cdrfiuba/tito/Placas/Placa_Tito_2011/Placa_1_sensor/placa1sensor.sch

## KiCad design Placas/Placa_Tito_2011/Placa_1_sensor/placa1sensor.sch (2011-11-02)

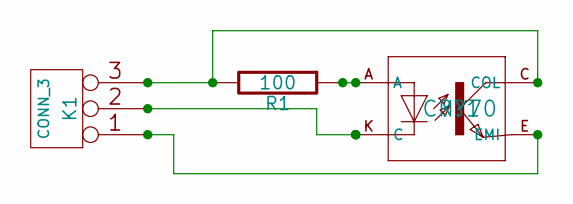
[picture p5: schematic placa1sensor.sch]

Parts:
??1: CNY70
K1: CONN_3
R1: 100

Connections:
unnamed: ??1.A, R1.1
unnamed: ??1.C (COL), K1.3, R1.2
unnamed: ??1.E (EMI), K1.1
unnamed: ??1.K (C), K1.2 (PM)
