cdrfiuba/tito/Placas/Placa_Tito_2011/Placa_principal/placa_principal.sch

## KiCad design Placas/Placa_Tito_2011/Placa_principal/placa_principal.sch (2013-02-23)

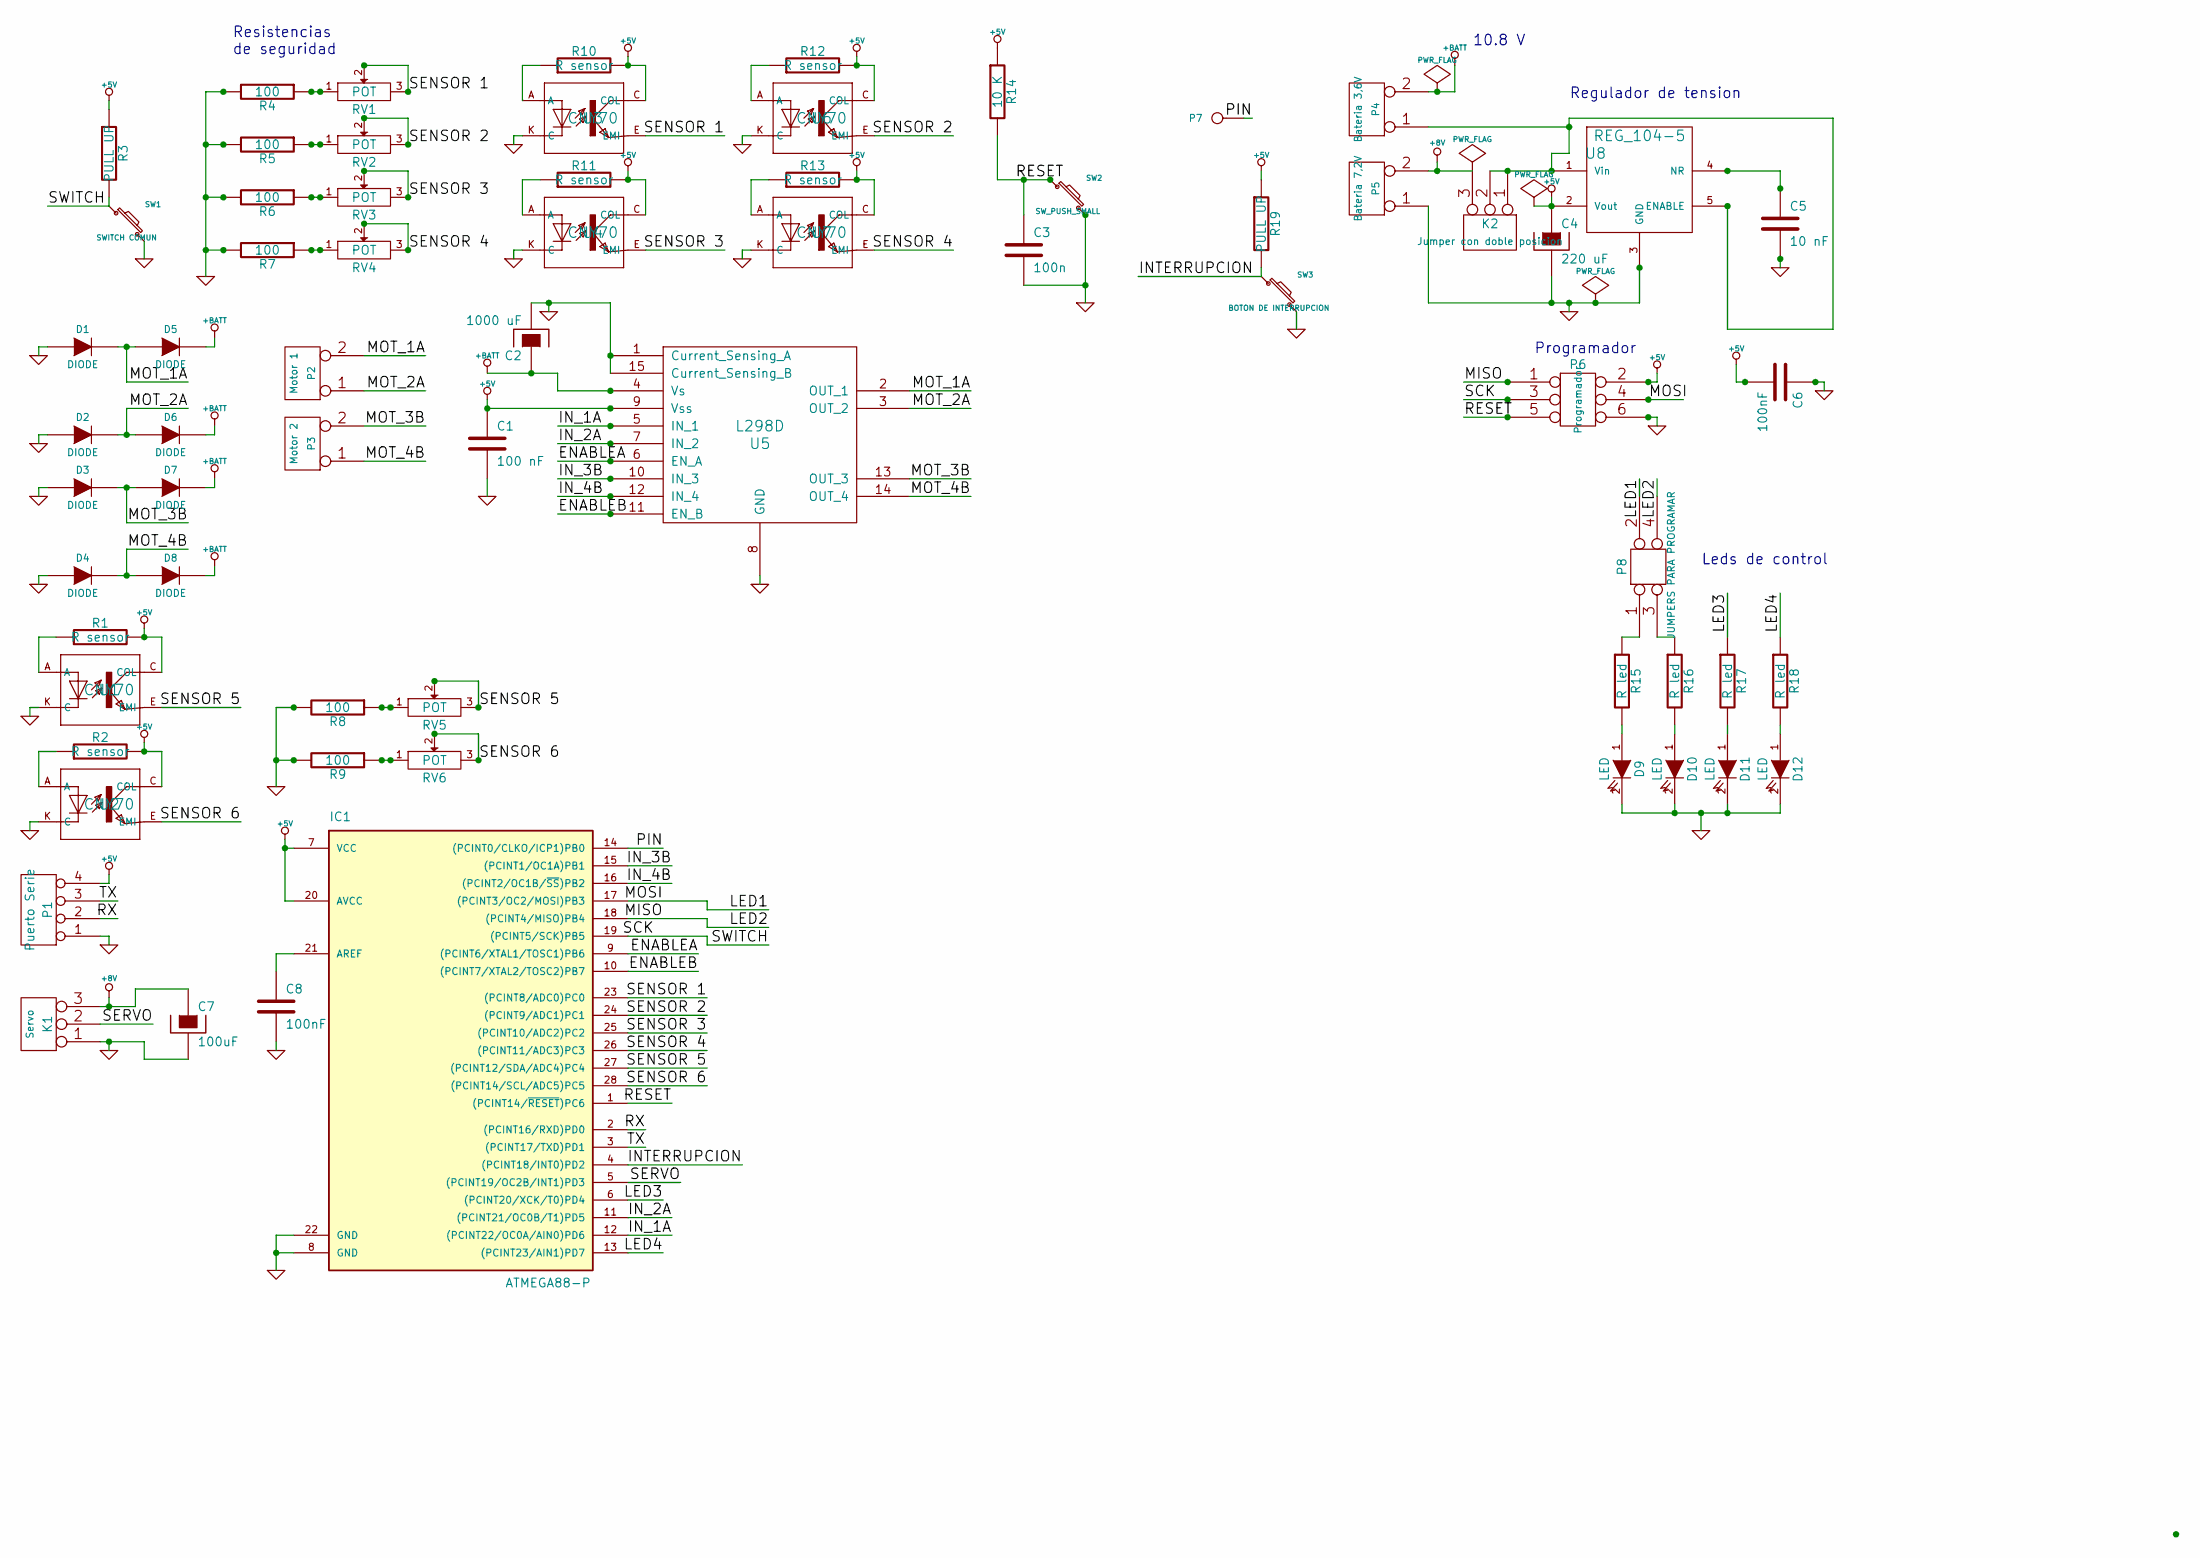
[picture p6: schematic placa_principal.sch]

Parts:
C1: 100 nF
C2: 1000 uF
C3: 100n
C4: 220 uF
C5: 10 nF
C6, C8: 100nF
C7: 100uF
D1, D2, D3, D4, D5, D6, D7, D8: DIODE
D9, D10, D11, D12: LED
IC1: ATMEGA88-P; DIL28
K1: Servo
K2: Jumper con doble posicion
P1: Puerto Serie
P2: Motor 1
P3: Motor 2
P4: Bateria 3,6V
P5: Bateria 7,2V
P6: Programador
P7: CONN_1
P8: JUMPERS PARA PROGRAMAR
R1, R2, R10, R11, R12, R13: R sensor
R3, R19: PULL UP
R4, R5, R6, R7, R8, R9: 100
R14: 10 K
R15, R16, R17, R18: R led
RV1, RV2, RV3, RV4, RV5, RV6: POT
SW1: SWITCH COMUN
SW2: SW_PUSH_SMALL
SW3: BOTON DE INTERRUPCION
U1, U2, U3, U4, U6, U7: CNY70
U5: L298D
U8: REG_104-5

Connections:
+5V: C1.1, C4.1, C6.2, IC1.7 (VCC), IC1.20 (AVCC), P1.4, P6.2, R1.2, R2.2, R3.1, R10.2, R11.2, R12.2, R13.2, R14.1, R19.1, U1.C (COL), U2.C (COL), U3.C (COL), U4.C (COL), U5.9 (Vss), U6.C (COL), U7.C (COL), U8.2 (Vout)
+8V: C7.1, K1.3, K2.3, P5.2 (PM)
+BATT: C2.1, D5.2 (K), D6.2 (K), D7.2 (K), D8.2 (K), P4.2 (PM), U5.4 (Vs)
ENABLEA: IC1.9 ((PCINT6/XTAL1/TOSC1)PB6), U5.6 (EN_A)
ENABLEB: IC1.10 ((PCINT7/XTAL2/TOSC2)PB7), U5.11 (EN_B)
GND: C1.2, C2.2, C3.2, C4.2, C5.2, C6.1, C7.2, C8.2, D1.1 (A), D2.1 (A), D3.1 (A), D4.1 (A), D9.2 (K), D10.2 (K), D11.2 (K), D12.2 (K), IC1.8 (GND), IC1.22 (GND), K1.1, P1.1, P5.1, P6.6, R4.2, R5.2, R6.2, R7.2, R8.2, R9.2, SW1.2, SW2.2, SW3.2, U1.K (C), U2.K (C), U3.K (C), U4.K (C), U5.1 (Current_Sensing_A), U5.8 (GND), U5.15 (Current_Sensing_B), U6.K (C), U7.K (C), U8.3 (GND)
INTERRUPCION: IC1.4 ((PCINT18/INT0)PD2), R19.2, SW3.1
IN_1A: IC1.12 ((PCINT22/OC0A/AIN0)PD6), U5.5 (IN_1)
IN_2A: IC1.11 ((PCINT21/OC0B/T1)PD5), U5.7 (IN_2)
IN_3B: IC1.15 ((PCINT1/OC1A)PB1), U5.10 (IN_3)
IN_4B: IC1.16 ((PCINT2/OC1B/~SS~)PB2), U5.12 (IN_4)
LED1: IC1.17 ((PCINT3/OC2/MOSI)PB3), P6.4, P8.2
LED2: IC1.18 ((PCINT4/MISO)PB4), P6.1, P8.4
LED3: IC1.6 ((PCINT20/XCK/T0)PD4), R17.1
LED4: IC1.13 ((PCINT23/AIN1)PD7), R18.1
MOT_1A: D1.2 (K), D5.1 (A), P2.2 (PM), U5.2 (OUT_1)
MOT_2A: D2.2 (K), D6.1 (A), P2.1, U5.3 (OUT_2)
MOT_3B: D3.2 (K), D7.1 (A), P3.2 (PM), U5.13 (OUT_3)
MOT_4B: D4.2 (K), D8.1 (A), P3.1, U5.14 (OUT_4)
unnamed: C5.1, U8.4 (NR)
unnamed: C8.1, IC1.21 (AREF)
unnamed: D9.1 (A), R15.2
unnamed: D10.1 (A), R16.2
unnamed: D11.1 (A), R17.2
unnamed: D12.1 (A), R18.2
unnamed: K2.1, K2.2 (PM), P4.1, U8.1 (Vin), U8.5 (ENABLE)
unnamed: P8.1, R15.1
unnamed: P8.3, R16.1
unnamed: R1.1, U1.A
unnamed: R2.1, U2.A
unnamed: R4.1, RV1.1
unnamed: R5.1, RV2.1
unnamed: R6.1, RV3.1
unnamed: R7.1, RV4.1
unnamed: R8.1, RV5.1
unnamed: R9.1, RV6.1
unnamed: R10.1, U3.A
unnamed: R11.1, U4.A
unnamed: R12.1, U6.A
unnamed: R13.1, U7.A
PIN: IC1.14 ((PCINT0/CLKO/ICP1)PB0), P7.1
RESET: C3.1, IC1.1 ((PCINT14/~RESET~)PC6), P6.5, R14.2, SW2.1
RX: IC1.2 ((PCINT16/RXD)PD0), P1.2
SCK: IC1.19 ((PCINT5/SCK)PB5), P6.3, R3.2, SW1.1
SENSOR 1: IC1.23 ((PCINT8/ADC0)PC0), RV1.2, RV1.3, U3.E (EMI)
SENSOR 2: IC1.24 ((PCINT9/ADC1)PC1), RV2.2, RV2.3, U6.E (EMI)
SENSOR 3: IC1.25 ((PCINT10/ADC2)PC2), RV3.2, RV3.3, U4.E (EMI)
SENSOR 4: IC1.26 ((PCINT11/ADC3)PC3), RV4.2, RV4.3, U7.E (EMI)
SENSOR 5: IC1.27 ((PCINT12/SDA/ADC4)PC4), RV5.2, RV5.3, U1.E (EMI)
SENSOR 6: IC1.28 ((PCINT14/SCL/ADC5)PC5), RV6.2, RV6.3, U2.E (EMI)
SERVO: IC1.5 ((PCINT19/OC2B/INT1)PD3), K1.2 (PM)
TX: IC1.3 ((PCINT17/TXD)PD1), P1.3

Notes on the sheet:
Programador
Resistencias de seguridad
10.8 V
Leds de control
Regulador de tension
