cdrfiuba/tito/SRC/Codigo Tito 2.0/tito.h

#ifndef HEADER_TITO
#define HEADER_TITO

/**
 Prototipos
*/
void startup (void);
//void prueba_frenado(void);

/**
 estados y eventos para la fsm
*/
typedef enum estados {
    
    ST_EN_LINEA = 0,

    ST_YENDOSE_POCO_POR_DERECHA = 1,
    ST_YENDOSE_MUCHO_POR_DERECHA = 2,
    ST_AFUERA_POR_DERECHA = 3,
    ST_VOLVIENDO_POR_DERECHA = 4,
    ST_VOLVIO_POR_DERECHA = 5,

    ST_YENDOSE_POCO_POR_IZQUIERDA = 6,
    ST_YENDOSE_MUCHO_POR_IZQUIERDA = 7,
    ST_AFUERA_POR_IZQUIERDA = 8,
    ST_VOLVIENDO_POR_IZQUIERDA = 9,
    ST_VOLVIO_POR_IZQUIERDA = 10,
    
    ST_MAX_ESTADOS = 11

} estados_t;
typedef enum estados_resumidos {
    EL=0,

    YPPD=1,
    YMPD=2,
    APD=3,
    VEPD=4,
    VOPD=5,

    YPPI=6,
    YMPI=7,
    API=8,
    VEPI=9,
    VOPI=10,

    ME=11
} estados_resumidos_t;
// (los sensores se componen como:
//  CURVA | S_IZQ | S_CEN | S_DER )
typedef enum eventos {
    EV_CUALQUIERA = 16,

    EV_SENSORES_NNNN = 0,
    EV_SENSORES_NNNB = 1,
    EV_SENSORES_NNBN = 2,
    EV_SENSORES_NNBB = 3,
    EV_SENSORES_NBNN = 4,
    EV_SENSORES_NBNB = 5,
    EV_SENSORES_NBBN = 6,
    EV_SENSORES_NBBB = 7,
    EV_SENSORES_BNNN = 8,
    EV_SENSORES_BNNB = 9,
    EV_SENSORES_BNBN = 10,
    EV_SENSORES_BNBB = 11,
    EV_SENSORES_BBNN = 12,
    EV_SENSORES_BBNB = 13,
    EV_SENSORES_BBBN = 14,
    EV_SENSORES_BBBB = 15,
    EV_MAX_SENSORES = 16
} eventos_t;

#define PORT_LED_1_NAME      C
#define LED_1_NUMBER         3
#define PORT_LED_1    def_port_reg(PORT_LED_1_NAME)
#define PIN_LED_1      def_pin_reg(PORT_LED_1_NAME)
#define DDR_LED_1      def_ddr_reg(PORT_LED_1_NAME)

#define PORT_LED_2_NAME      C
#define LED_2_NUMBER         2
#define PORT_LED_2    def_port_reg(PORT_LED_2_NAME)
#define PIN_LED_2      def_pin_reg(PORT_LED_2_NAME)
#define DDR_LED_2      def_ddr_reg(PORT_LED_2_NAME)

#define PORT_LED_3_NAME      C
#define LED_3_NUMBER         1
#define PORT_LED_3    def_port_reg(PORT_LED_3_NAME)
#define PIN_LED_3      def_pin_reg(PORT_LED_3_NAME)
#define DDR_LED_3      def_ddr_reg(PORT_LED_3_NAME)

#define PORT_LED_4_NAME      C
#define LED_4_NUMBER         0
#define PORT_LED_4    def_port_reg(PORT_LED_4_NAME)
#define PIN_LED_4      def_pin_reg(PORT_LED_4_NAME)
#define DDR_LED_4      def_ddr_reg(PORT_LED_4_NAME)

#define PORT_SENSOR_1_NAME      D
#define SENSOR_1_NUMBER         5
#define PORT_SENSOR_1    def_port_reg(PORT_SENSOR_1_NAME)
#define PIN_SENSOR_1      def_pin_reg(PORT_SENSOR_1_NAME)
#define DDR_SENSOR_1      def_ddr_reg(PORT_SENSOR_1_NAME)

#define PORT_SENSOR_2_NAME      D
#define SENSOR_2_NUMBER         6
#define PORT_SENSOR_2    def_port_reg(PORT_SENSOR_2_NAME)
#define PIN_SENSOR_2      def_pin_reg(PORT_SENSOR_2_NAME)
#define DDR_SENSOR_2      def_ddr_reg(PORT_SENSOR_2_NAME)

#define PORT_SENSOR_3_NAME      D
#define SENSOR_3_NUMBER         7
#define PORT_SENSOR_3    def_port_reg(PORT_SENSOR_3_NAME)
#define PIN_SENSOR_3      def_pin_reg(PORT_SENSOR_3_NAME)
#define DDR_SENSOR_3      def_ddr_reg(PORT_SENSOR_3_NAME)

#define PORT_SENSOR_CURVA_NAME      D
#define SENSOR_CURVA_NUMBER         2
#define PORT_SENSOR_CURVA    def_port_reg(PORT_SENSOR_CURVA_NAME)
#define PIN_SENSOR_CURVA      def_pin_reg(PORT_SENSOR_CURVA_NAME)
#define DDR_SENSOR_CURVA      def_ddr_reg(PORT_SENSOR_CURVA_NAME)

#define PORT_BOTON_NAME      B
#define BOTON_NUMBER         0
#define PORT_BOTON       def_port_reg(PORT_BOTON_NAME)
#define PIN_BOTON         def_pin_reg(PORT_BOTON_NAME)
#define DDR_BOTON            def_ddr_reg(PORT_BOTON_NAME)

#define SetBit(Byte,Bit)       (Byte |= (1<<Bit))
#define ClearBit(Byte,Bit)     (Byte &= (~(1<<Bit)))
#define IsBitSet(Byte,Bit)     ((Byte&(1<<Bit)) ? 1 : 0)
//#define IsBitSet(Byte,Bit)     ((Byte>>Bit) & 1)

#define SENSOR_IZQUIERDA    IsBitSet(PIN_SENSOR_1, SENSOR_1_NUMBER)
#define SENSOR_CENTRO        IsBitSet(PIN_SENSOR_2, SENSOR_2_NUMBER)
#define SENSOR_DERECHA        IsBitSet(PIN_SENSOR_3, SENSOR_3_NUMBER)
#define SENSOR_CURVA        IsBitSet(PIN_SENSOR_CURVA, SENSOR_CURVA_NUMBER)

#define BOTON_APRETADO         (!(PINB&(1<<PB0)))
#define BOTON_NO_APRETADO     (PINB&(1<<PB0))

#define FACTOR 1 // coeficiente de disminuición de velocidad

#define ESTADO_SENSORES ((SENSOR_CURVA << 3) | (SENSOR_IZQUIERDA << 2) | (SENSOR_CENTRO << 1) | (SENSOR_DERECHA))

#define COEFICIENTE_DERECHA 0.5
#define COEFICIENTE_IZQUIERDA 0.5
#define ACTIVAR_PROPULSORES_TRASEROS 1
#define USAR_FRENOS(us_ad, us_at) PWM1_VEL(100);PWM2_VEL(100);mot1_sent(AD);mot2_sent(AD);_delay_us(us_ad);mot1_sent(AT);mot2_sent(AT);_delay_us(us_at);

/*
#define concat(a,b)        a ## b
#define def_port_reg(name)    concat(PORT,name)
#define def_pin_reg(name)    concat(PIN,name)
#define def_ddr_reg(name)    concat(DDR,name)
*/
#endif
